macnamtran/TLV767_LDO/simulation/load_transient_10mA_100mA/TLV76701_TRANS-PSpiceFiles/STARTUP/trans/trans.cir

** Profile: "STARTUP-trans"  [ C:\Users\User\Downloads\load_transient_10mA_100mA\tlv76701_trans-pspicefiles\startup\trans.sim ] 

** Creating circuit file "trans.cir" 
** WARNING: THIS AUTOMATICALLY GENERATED FILE MAY BE OVERWRITTEN BY SUBSEQUENT SIMULATIONS

*Libraries: 
* Profile Libraries :
* Local Libraries :
.LIB "../../../tlv76701_trans.lib" 
* From [PSPICE NETLIST] section of C:\cds_spb_home\cdssetup\OrCAD_PSpiceTIPSpice_Install\23.1.0\PSpice.ini file:
.lib "nom_pspti.lib" 
.lib "nom.lib" 

*Analysis directives: 
.TRAN  0 5m 0 0.1u 
.OPTIONS ADVCONV
.OPTIONS FILEMODELSEARCH
.OPTIONS TNOM= 25.0
.PROBE64 V(alias(*)) I(alias(*)) W(alias(*)) D(alias(*)) NOISE(alias(*)) 
.INC "..\STARTUP.net" 


.END
