macnamtran/TLV767_LDO/simulation/load_transient_10mA_100mA/load_step_10to100mA_dip.png

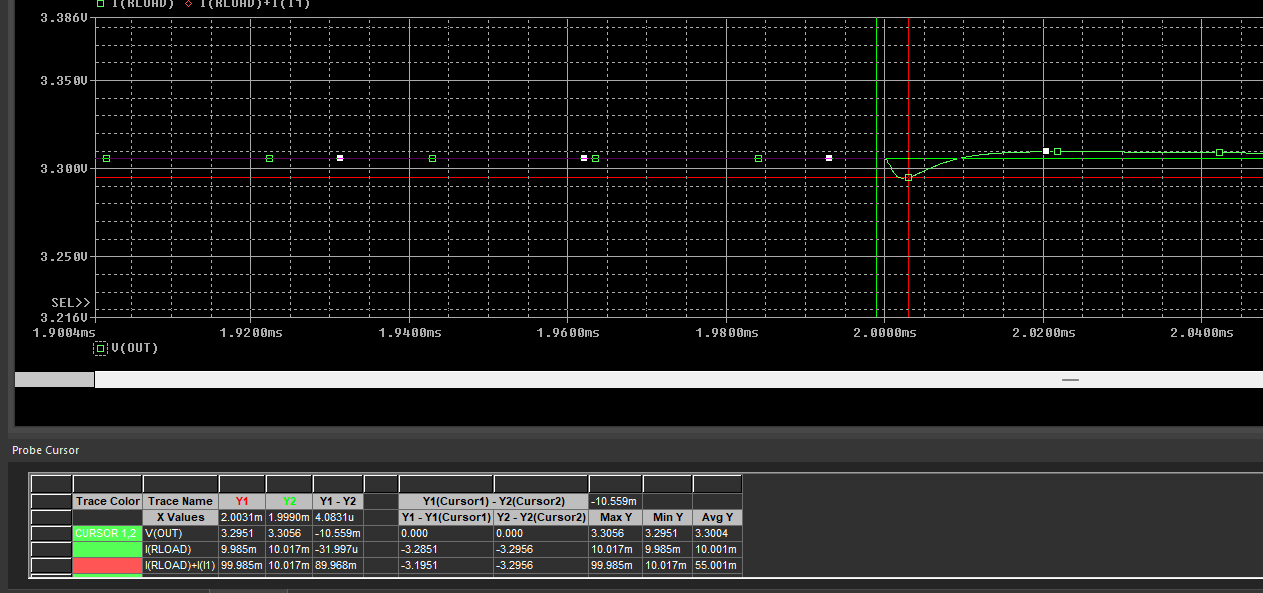
simulation/load_transient_10mA_100mA/load_step_10to100mA_dip.png
